gfr10598/encoder-wheel/data_sim/angular_velocity_trace.png

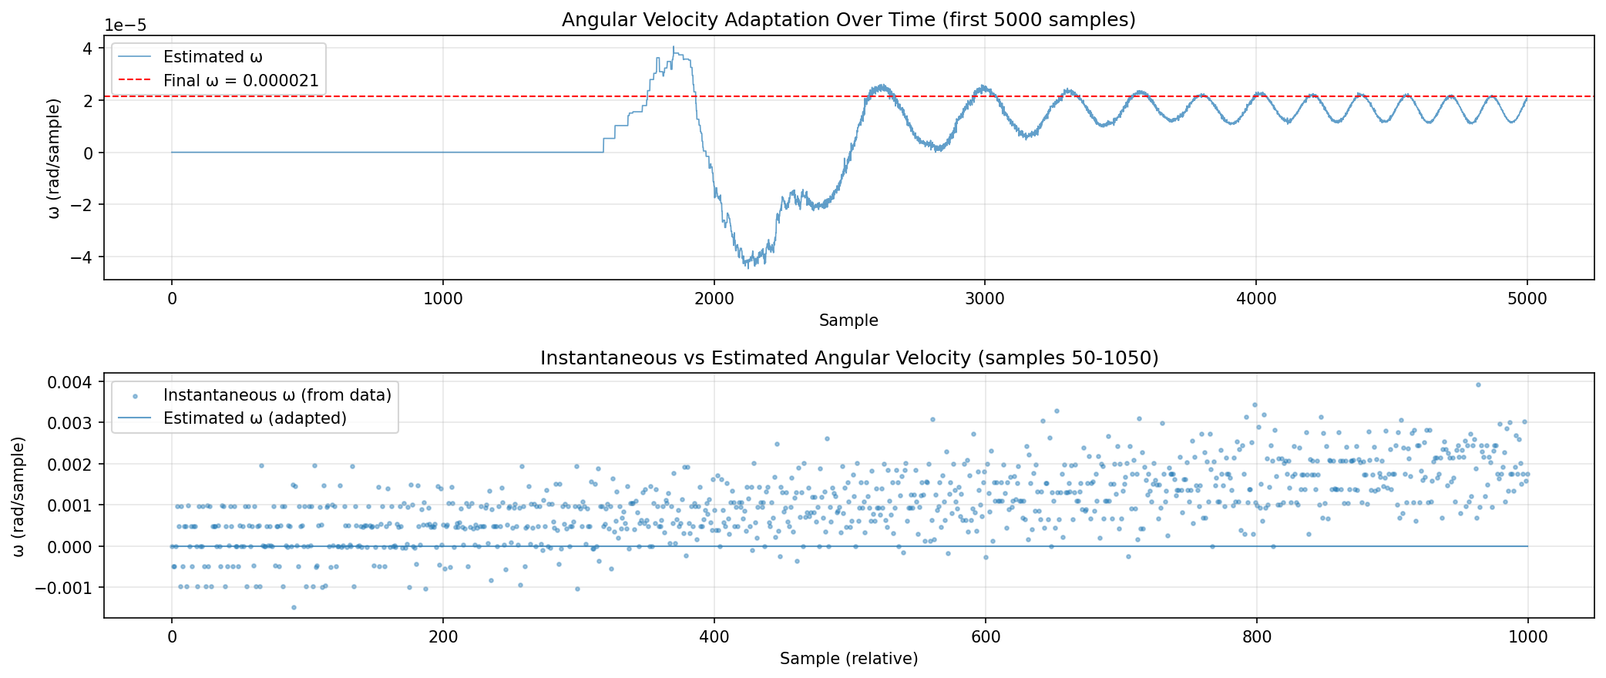
data_sim/angular_velocity_trace.png
