gfr10598/encoder-wheel/data_sim/coupled_predictors_comparison.png

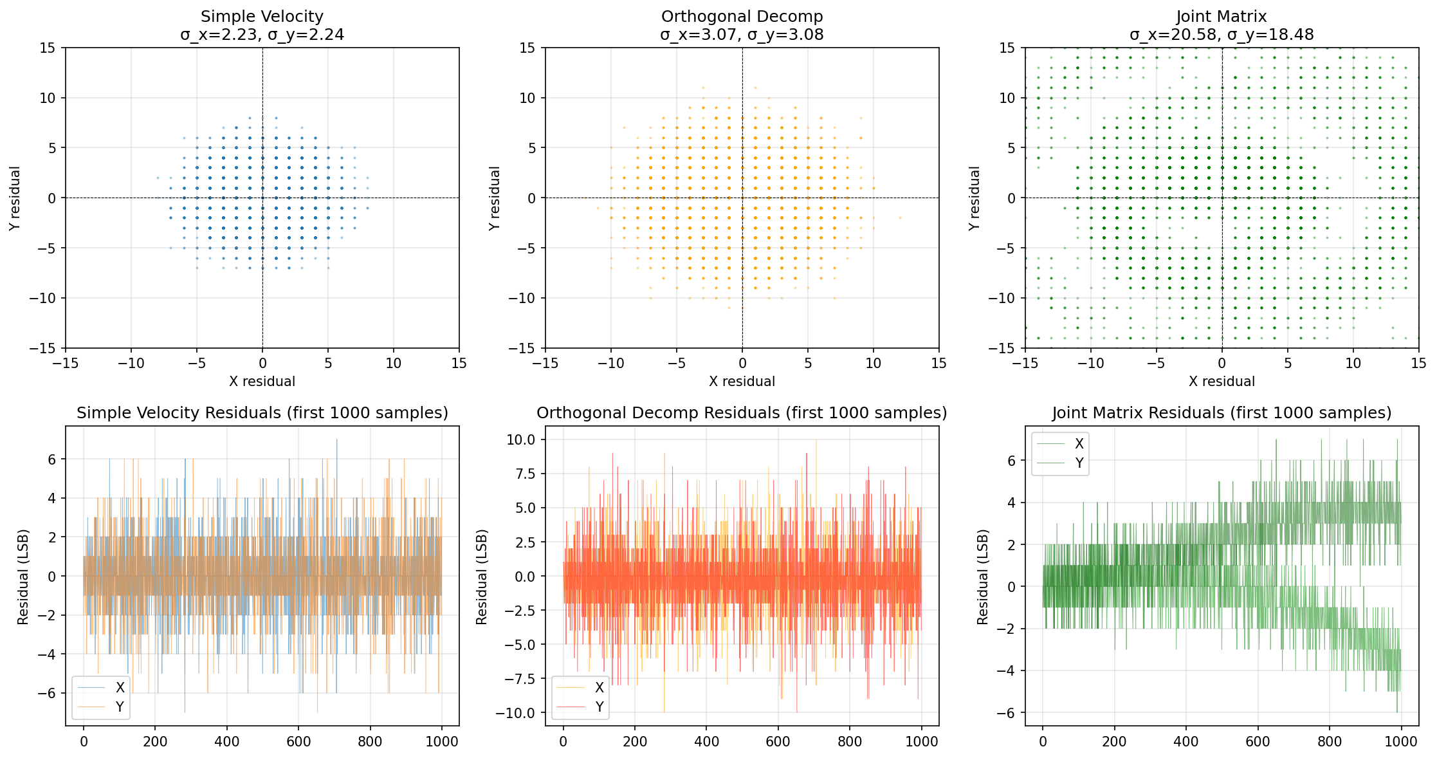
data_sim/coupled_predictors_comparison.png
