gfr10598/encoder-wheel/examples/plots/raw_B_400.png

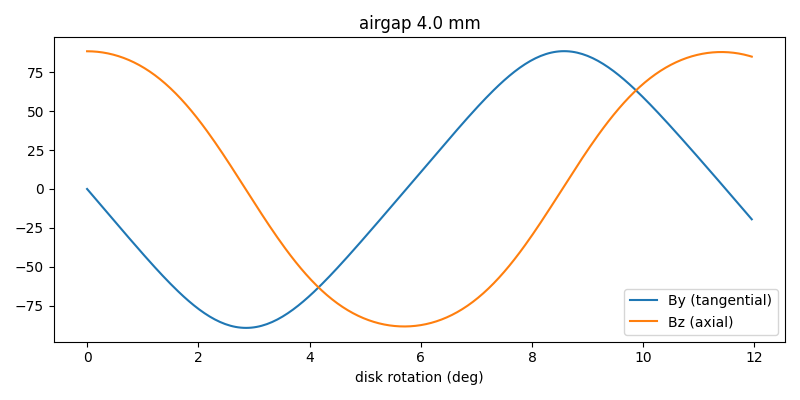
examples/plots/raw_B_400.png
