gfr10598/encoder-wheel/scripts/magnetic/4/4magnet_amplitude_thd.png

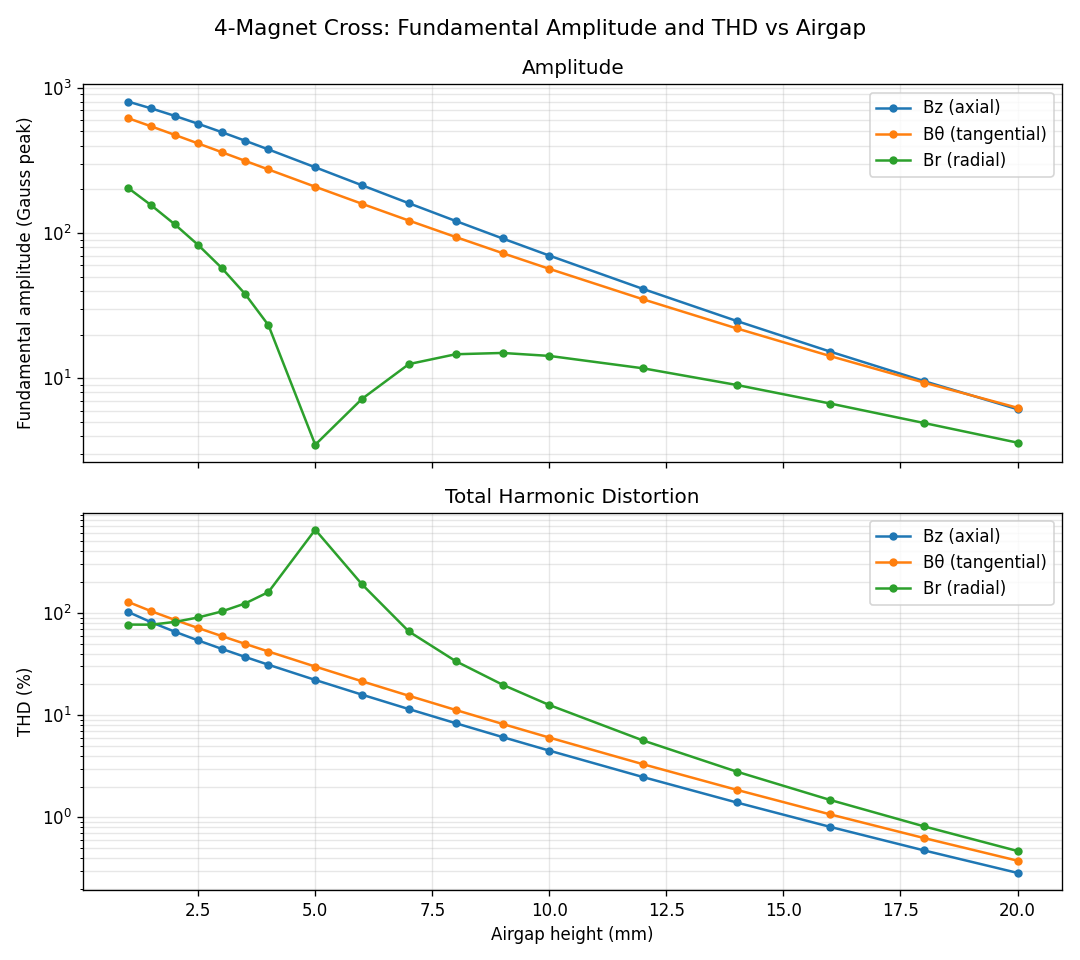
scripts/magnetic/4/4magnet_amplitude_thd.png
