gfr10598/encoder-wheel/scripts/magnetic/10/10mag_amplitude_thd.png

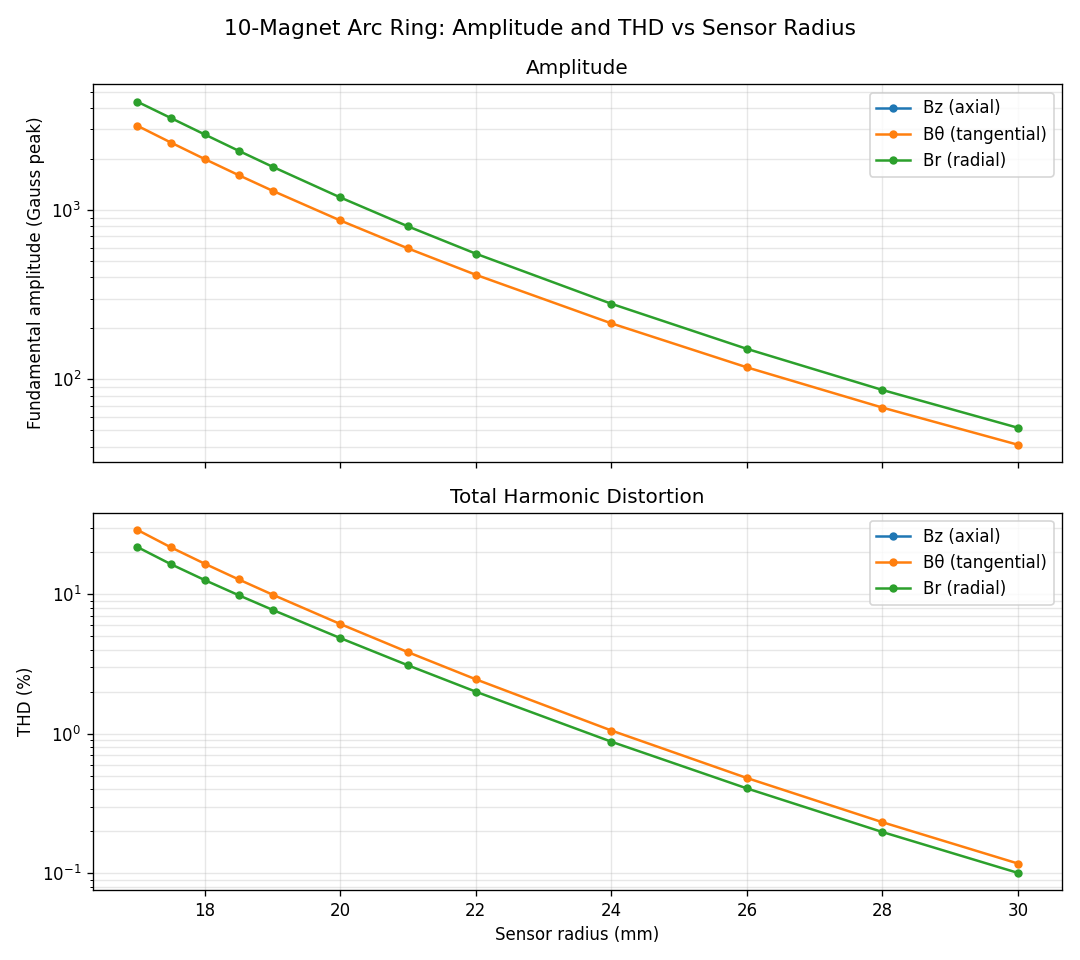
scripts/magnetic/10/10mag_amplitude_thd.png
