gfr10598/encoder-wheel/scripts/magnetic/16/16mag_amplitude_thd.png

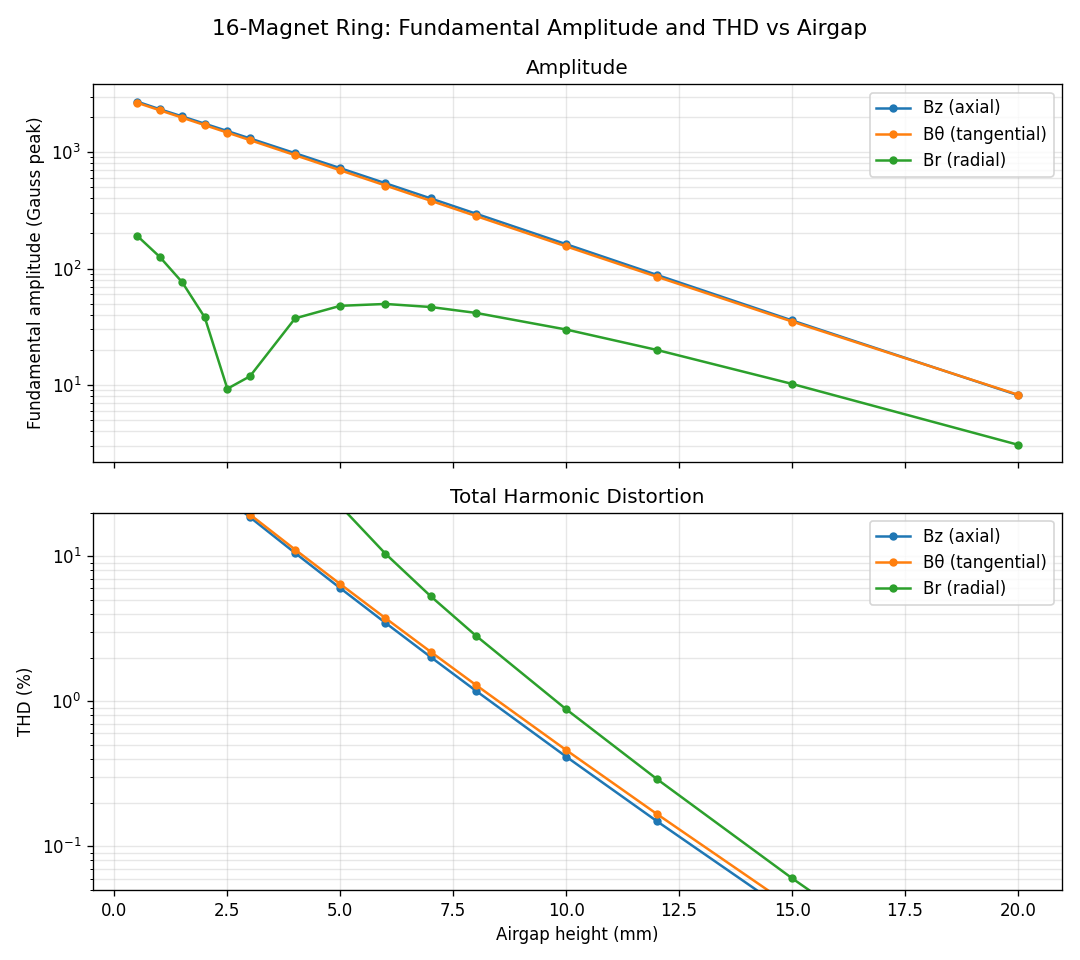
scripts/magnetic/16/16mag_amplitude_thd.png
