gfr10598/encoder-wheel/scripts/magnetic/26/26mag_amplitude_thd.png

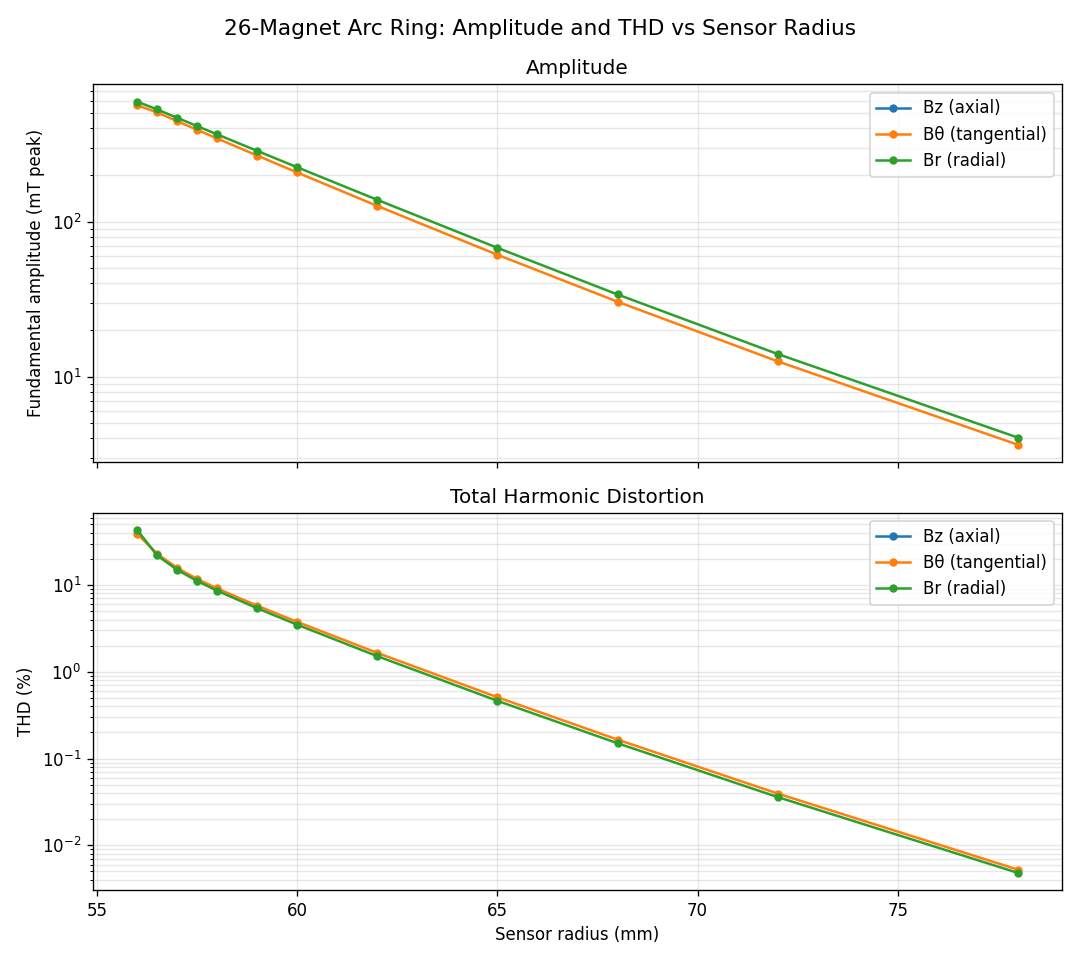
scripts/magnetic/26/26mag_amplitude_thd.png
