gfr10598/encoder-wheel/scripts/magnetic/90/90mag_amplitude_thd.png

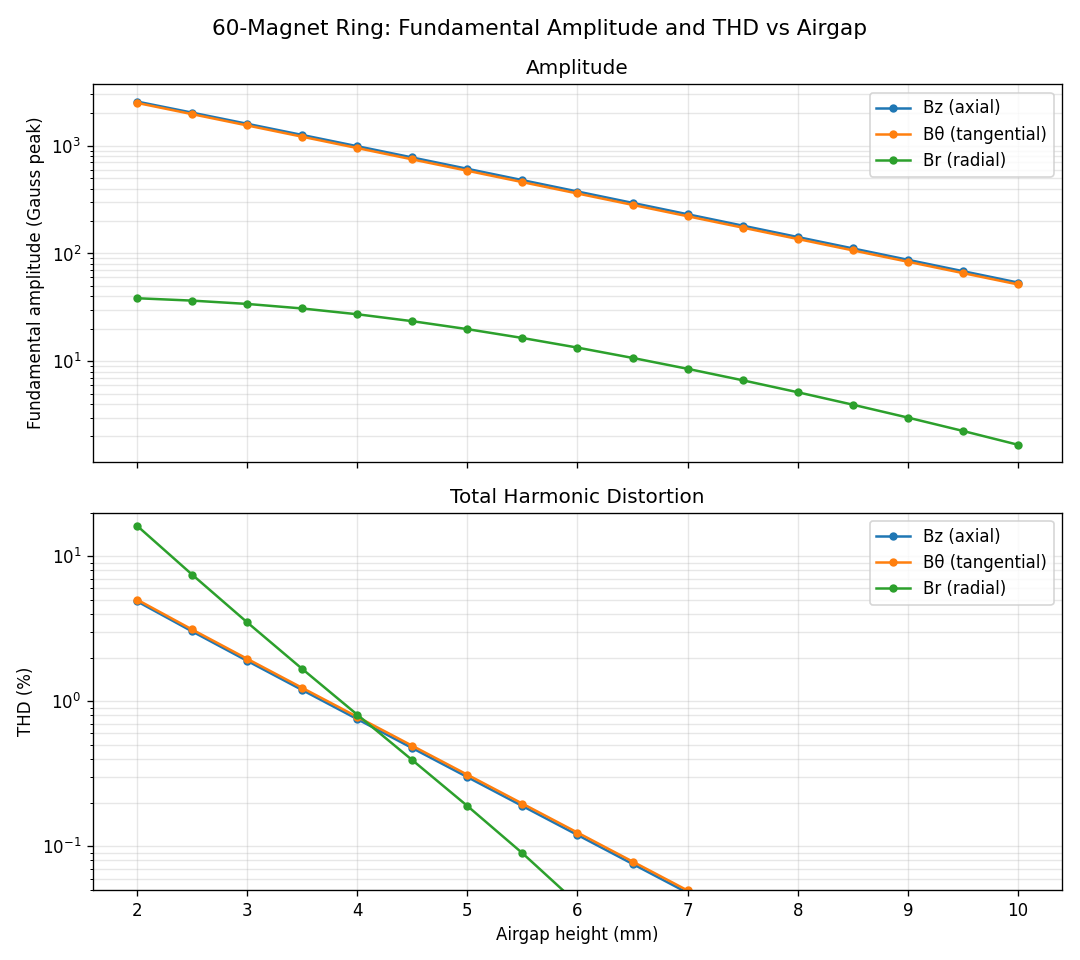
scripts/magnetic/90/90mag_amplitude_thd.png
