gfr10598/encoder-wheel/examples/plots/tmp_compare_components.png

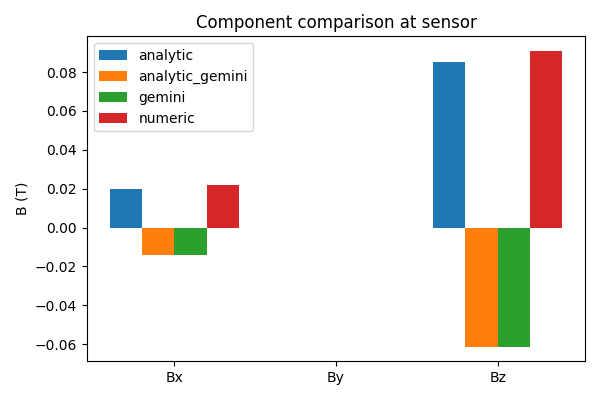
examples/plots/tmp_compare_components.png
