gfr10598/encoder-wheel/examples/plots/test_single_airgap_4mm.png

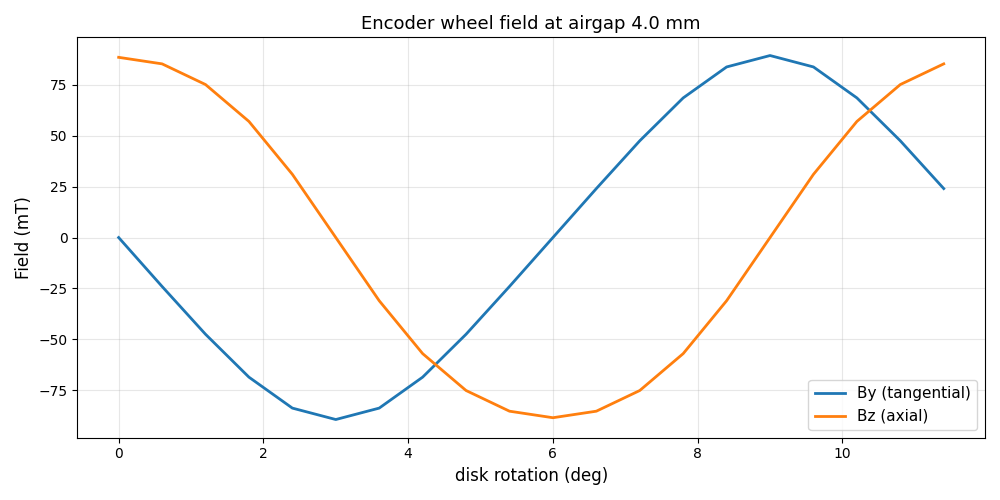
examples/plots/test_single_airgap_4mm.png
