gfr10598/encoder-wheel/examples/configs/n52_20x8x1.5_60_outer4in_sensor3p8in_fine.yaml

n_magnets: 60
magnet_dims_mm: [20.0, 8.0, 1.5]
Br_T: 1.45
outer_radius_mm: 101.6
sensor_radius_mm: 96.52
airgap_min_mm: 0.5
airgap_max_mm: 8.0
airgap_steps: 16
theta_steps: 768
theta_sweep_deg: 12.0
model: discrete
discrete_grid: [40,16,3]
outdir: examples/plots
summary_path: examples/plots/summary_n52_60_fine.json
steel_backing_thickness_mm: 3.175
steel_mu_r: 5.7
